Tobias-DG3YEV/RA-Sentinel/RASBB/Hardware/Rev.C/Design/Footprints/MMSZ5255BT1G.stp

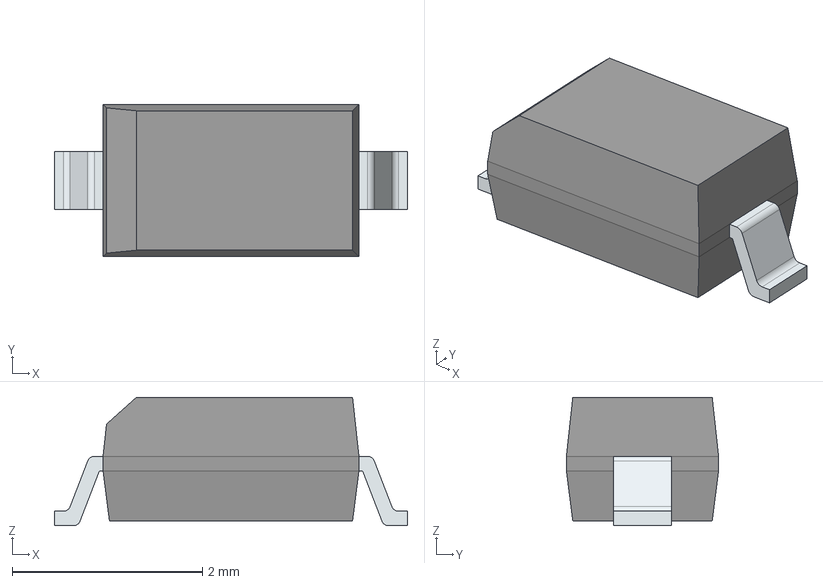
[picture p32: CAD file, 2026-08-13]
RASBB/Hardware/Rev.C/Design/Footprints/MMSZ5255BT1G.stp
3.71 x 1.60 x 1.35 mm
FilletPinL
FilletPinR
