Tobias-DG3YEV/RA-Sentinel/RASBB/Hardware/Rev.C/Design/Footprints/B340LB-13-F.stp

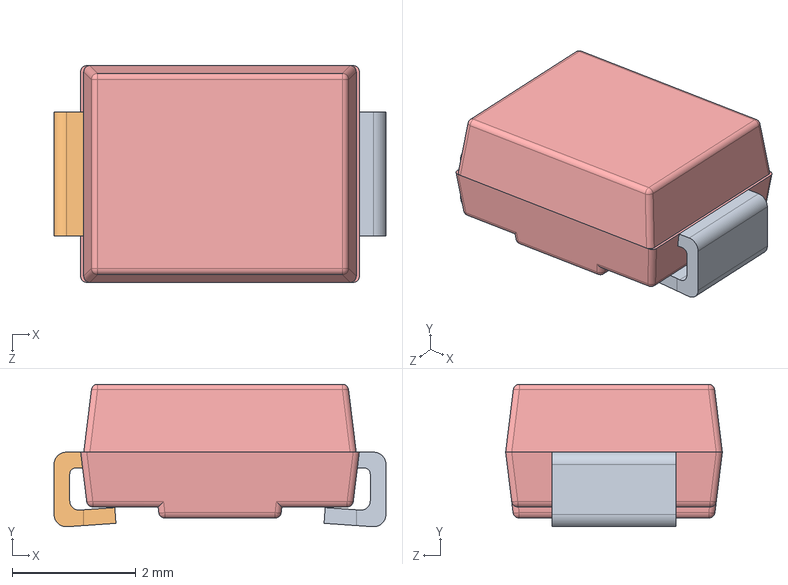
[picture p33: CAD file, 2026-08-13]
RASBB/Hardware/Rev.C/Design/Footprints/B340LB-13-F.stp
5.36 x 2.30 x 3.50 mm
LF 63010000599 RS2M
70mil 240 um RGPP
clip 63010000719 SQ0.45 H0.64 RS2M
SMB 16R compound RS2M
錨璃2^RS2M
