Tobias-DG3YEV/RA-Sentinel/RASBB/Hardware/Rev.C/Design/Footprints/VSSAF5L45HM3_A_H.stp

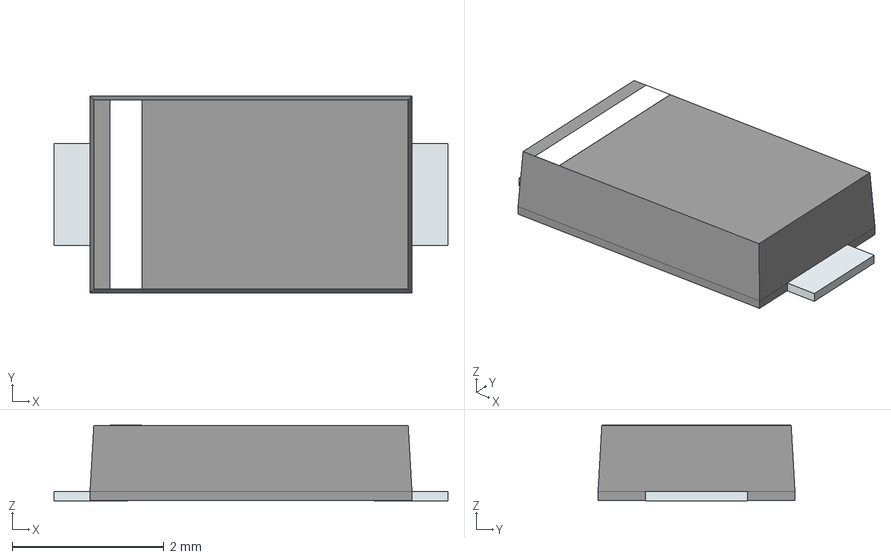
[picture p34: CAD file, 2026-08-13]
RASBB/Hardware/Rev.C/Design/Footprints/VSSAF5L45HM3_A_H.stp
5.20 x 2.60 x 1.00 mm
PinKIdent
PinK
PinA
