Tobias-DG3YEV/RA-Sentinel/RASBB/Hardware/Rev.C/Design/Footprints/BLM15BD601SH1D.stp

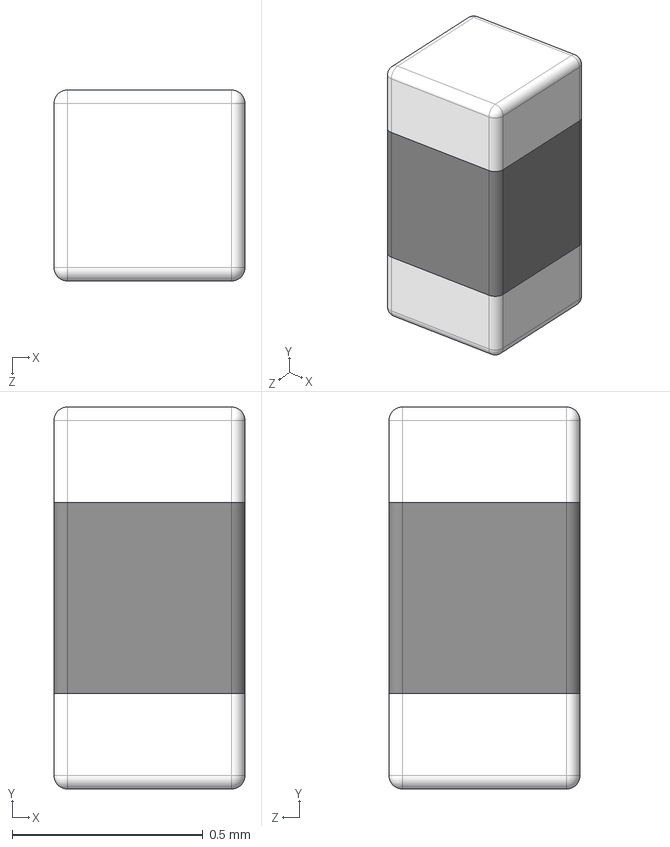
[picture p35: CAD file, 2026-08-13]
RASBB/Hardware/Rev.C/Design/Footprints/BLM15BD601SH1D.stp
0.5 x 1.00 x 0.5 mm
