Tobias-DG3YEV/RA-Sentinel/RASBB/Hardware/Rev.C/Design/Footprints/TS3A5018DBQR.stp

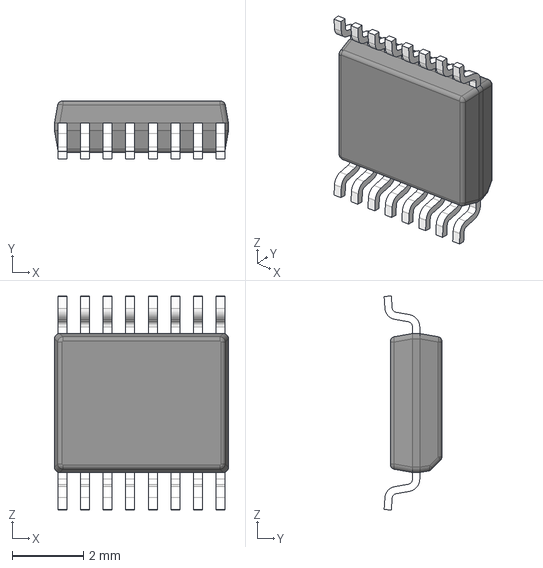
[picture p36: CAD file, 2026-08-13]
RASBB/Hardware/Rev.C/Design/Footprints/TS3A5018DBQR.stp
4.90 x 1.63 x 6.02 mm
BODY-SO
LEAD-DBQ0016B x 16
