Tobias-DG3YEV/RA-Sentinel/RASBB/Hardware/Rev.C/Design/Footprints/SDT5A60SA-13.stp

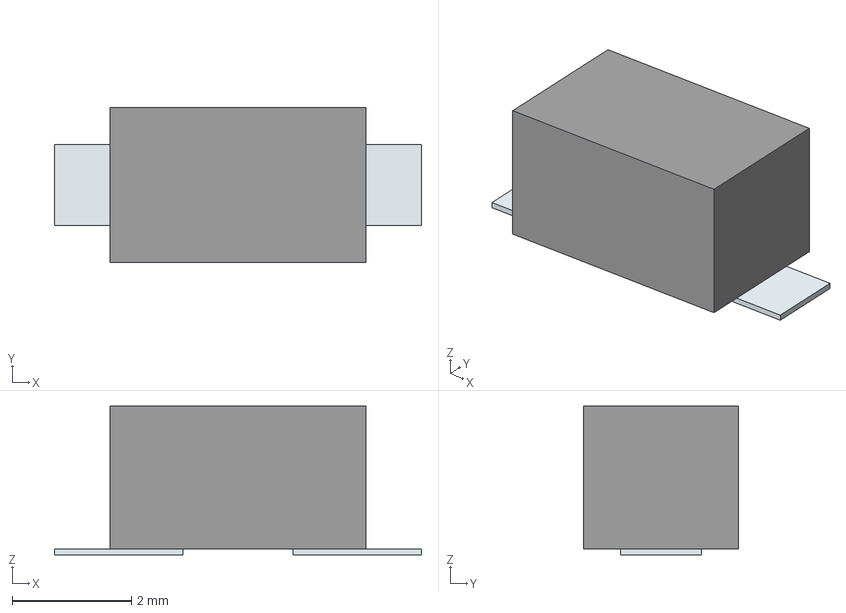
[picture p37: CAD file, 2026-08-13]
RASBB/Hardware/Rev.C/Design/Footprints/SDT5A60SA-13.stp
6.16 x 2.61 x 2.50 mm
Pins
