Tobias-DG3YEV/RA-Sentinel/RASBB/Hardware/Rev.C/Design/Footprints/SW_Wurth_WS-TASV_435451019820.step

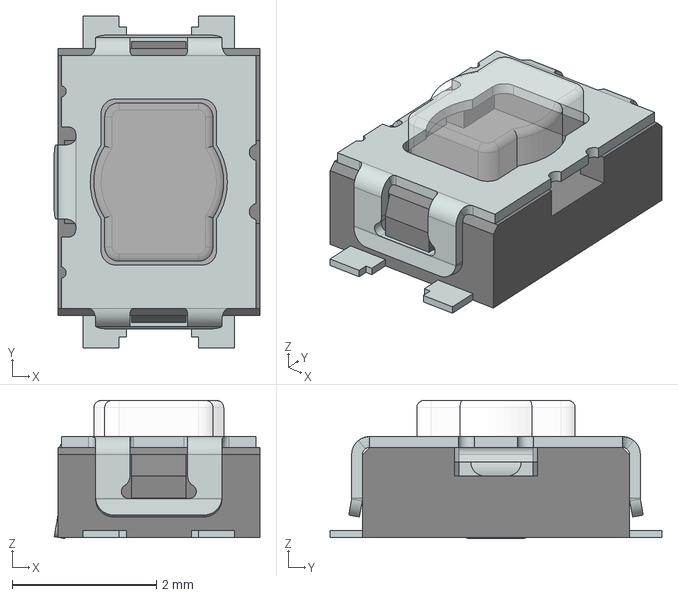
[picture p38: CAD file, 2026-08-13]
RASBB/Hardware/Rev.C/Design/Footprints/SW_Wurth_WS-TASV_435451019820.step
2.85 x 4.60 x 1.91 mm
