Tobias-DG3YEV/RA-Sentinel/RASBB/Hardware/Rev.C/Design/Footprints/XC7A100T-2CSG324I.stp

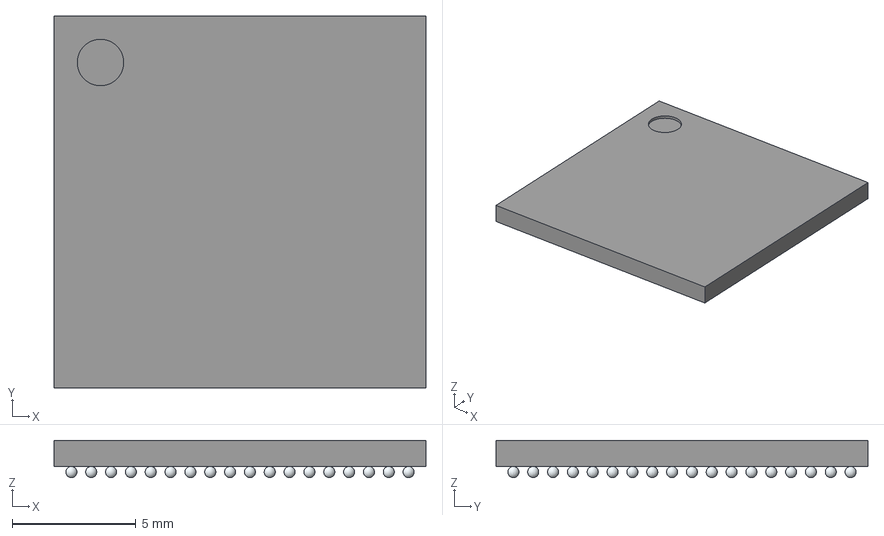
[picture p40: CAD file, 2026-08-13]
RASBB/Hardware/Rev.C/Design/Footprints/XC7A100T-2CSG324I.stp
15.0 x 15.0 x 1.50 mm
