Tobias-DG3YEV/RA-Sentinel/RASBB/Hardware/Rev.C/Design/Footprints/STP_MJ_HORIZONTAL_SHIELDED_W_LED _8P8C_TAB_UP_THR_615108137221R (rev1).stp

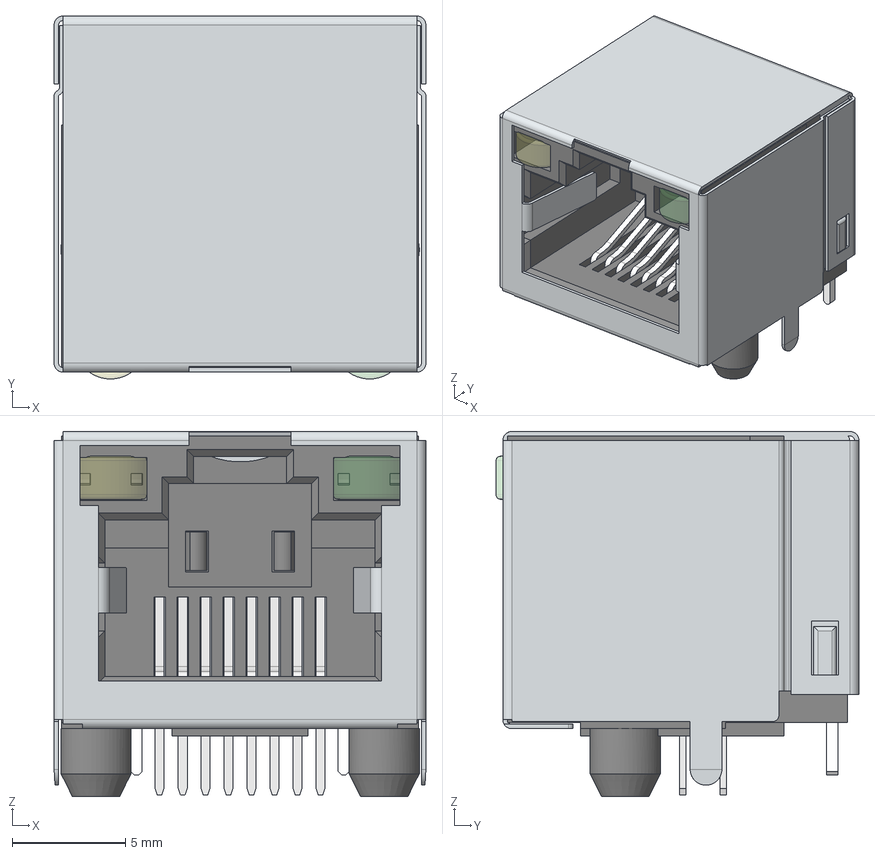
[picture p41: CAD file, 2026-08-13]
RASBB/Hardware/Rev.C/Design/Footprints/STP_MJ_HORIZONTAL_SHIELDED_W_LED _8P8C_TAB_UP_THR_615108137221R (rev1).stp
16.4 x 16.0 x 16.1 mm
615108137221R_Shielding
615108137221R_Housing
615108137221R_Pin Longue x 4
615108137221R_Pin Short x 4
615108137221R_Housing-2
615108137221R_Led Green
615108137221R_Led Yellow
