Tobias-DG3YEV/RA-Sentinel/RASBB/Software/RASBB_ECU/Core/Inc/lwipopts.h

/**
 * Copyright (C) 2017, STMicroelectronics, all right reserved.
 * Copyright (c) 2001-2004 Swedish Institute of Computer Science.
 * All rights reserved.
 *
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
 * This file is part of the lwIP TCP/IP stack.
 *
 * Author: Adam Dunkels <adam@sics.se>
 ******************************************************************************
 */

#ifndef __LWIPOPTS_H__
#define __LWIPOPTS_H__

/**
 * NO_SYS==1: Provides VERY minimal functionality. Otherwise,
 * use lwIP facilities.
 */
#define NO_SYS                  0

/*---------- Debug flags -----------*/
#define 	ETHARP_DEBUG    LWIP_DBG_OFF
#define 	UDP_DEBUG       LWIP_DBG_ON
#define PBUF_DEBUG        LWIP_DBG_OFF
#define MEM_STATS         1
#define   SO_REUSE        0

/* ---------- Memory options ---------- */
/* MEM_ALIGNMENT: should be set to the alignment of the CPU for which
   lwIP is compiled. 4 byte alignment -> define MEM_ALIGNMENT to 4, 2
   byte alignment -> define MEM_ALIGNMENT to 2. */
#define MEM_ALIGNMENT           4

/* MEM_SIZE: the size of the heap memory. If the application will send
a lot of data that needs to be copied, this should be set high. */
#define MEM_SIZE                (24*1024)

/* Relocate the LwIP RAM heap pointer */
#define LWIP_RAM_HEAP_POINTER    (0x30004000)

/* MEMP_NUM_TCP_PCB: the number of simulatenously active TCP
   connections. */
#define MEMP_NUM_TCP_PCB        20

#define MEMP_NUM_NETCONN		8

/* MEMP_NUM_TCP_SEG: the number of simultaneously queued TCP
   segments. */
#define MEMP_NUM_TCP_SEG        TCP_SND_QUEUELEN

/* ---------- Pbuf options ---------- */
/* PBUF_POOL_SIZE: the number of buffers in the pbuf pool.
   @ note: used to allocate Tx pbufs only */

/* PBUF_POOL_BUFSIZE: the size of each pbuf in the pbuf pool. */
#define PBUF_POOL_BUFSIZE       1536

/* LWIP_SUPPORT_CUSTOM_PBUF == 1: to pass directly MAC Rx buffers to the stack
   no copy is needed */
#define LWIP_SUPPORT_CUSTOM_PBUF      1

/* ---------- IPv4 options ---------- */
#define LWIP_IPV4                1

/* ---------- TCP options ---------- */
#define LWIP_TCP                1
#define TCP_TTL                 255

/* Controls if TCP should queue segments that arrive out of
   order. Define to 0 if your device is low on memory. */

/* TCP Maximum segment size. */
#define TCP_MSS                 (1500 - 40)	  /* TCP_MSS = (Ethernet MTU - IP header size - TCP header size) */

/* TCP sender buffer space (bytes). */
#define TCP_SND_BUF             (4*TCP_MSS)


/* TCP receive window. */
#define TCP_WND                 (4*TCP_MSS)


/* ---------- ICMP options ---------- */
#define LWIP_ICMP                       1


/* ---------- DHCP options ---------- */
#define LWIP_DHCP               0


/* ---------- UDP options ---------- */
#define LWIP_UDP                1
#define UDP_TTL                 255

#define LWIP_IGMP                       1

/* ---------- Statistics options ---------- */
#define LWIP_STATS 				1

/* ---------- link callback options ---------- */
/* LWIP_NETIF_LINK_CALLBACK==1: Support a callback function from an interface
 * whenever the link changes (i.e., link down)
 */
#define LWIP_NETIF_LINK_CALLBACK        0

/*
   --------------------------------------
   ---------- Checksum options ----------
   --------------------------------------
*/

/*
The STM32H7xx allows computing and verifying the IP, UDP, TCP and ICMP checksums by hardware:
 - To use this feature let the following define uncommented.
 - To disable it and process by CPU comment the  the checksum.
*/
#define CHECKSUM_BY_HARDWARE


#ifdef CHECKSUM_BY_HARDWARE
  /* CHECKSUM_GEN_IP==0: Generate checksums by hardware for outgoing IP packets.*/
  #define CHECKSUM_GEN_IP                 0
  /* CHECKSUM_GEN_UDP==0: Generate checksums by hardware for outgoing UDP packets.*/
  #define CHECKSUM_GEN_UDP                0
  /* CHECKSUM_GEN_TCP==0: Generate checksums by hardware for outgoing TCP packets.*/
  #define CHECKSUM_GEN_TCP                0
  /* CHECKSUM_CHECK_IP==0: Check checksums by hardware for incoming IP packets.*/
  #define CHECKSUM_CHECK_IP               0
  /* CHECKSUM_CHECK_UDP==0: Check checksums by hardware for incoming UDP packets.*/
  #define CHECKSUM_CHECK_UDP              0
  /* CHECKSUM_CHECK_TCP==0: Check checksums by hardware for incoming TCP packets.*/
  #define CHECKSUM_CHECK_TCP              0
  /* CHECKSUM_GEN_ICMP==1: Check checksums by hardware for outgoing ICMP packets.*/
  /* Hardware TCP/UDP checksum insertion not supported when packet is an IPv4 fragment */
  #define CHECKSUM_GEN_ICMP               1
  /* CHECKSUM_CHECK_ICMP==0: Check checksums by hardware for incoming ICMP packets.*/
  #define CHECKSUM_CHECK_ICMP             0

#else
  /* CHECKSUM_GEN_IP==1: Generate checksums in software for outgoing IP packets.*/
  #define CHECKSUM_GEN_IP                 1
  /* CHECKSUM_GEN_UDP==1: Generate checksums in software for outgoing UDP packets.*/
  #define CHECKSUM_GEN_UDP                1
  /* CHECKSUM_GEN_TCP==1: Generate checksums in software for outgoing TCP packets.*/
  #define CHECKSUM_GEN_TCP                1
  /* CHECKSUM_CHECK_IP==1: Check checksums in software for incoming IP packets.*/
  #define CHECKSUM_CHECK_IP               1
  /* CHECKSUM_CHECK_UDP==1: Check checksums in software for incoming UDP packets.*/
  #define CHECKSUM_CHECK_UDP              1
  /* CHECKSUM_CHECK_TCP==1: Check checksums in software for incoming TCP packets.*/
  #define CHECKSUM_CHECK_TCP              1
  /* CHECKSUM_GEN_ICMP==1: Check checksums by hardware for outgoing ICMP packets.*/
  #define CHECKSUM_GEN_ICMP               1
  /* CHECKSUM_CHECK_ICMP==1: Check checksums by hardware for incoming ICMP packets.*/
  #define CHECKSUM_CHECK_ICMP             1
#endif


/*
   ----------------------------------------------
   ---------- Sequential layer options ----------
   ----------------------------------------------
*/
/**
 * LWIP_NETCONN==1: Enable Netconn API (require to use api_lib.c)
 */
#define LWIP_NETCONN                    1

/*
   ------------------------------------
   ---------- Socket options ----------
   ------------------------------------
*/
/**
 * LWIP_SOCKET==1: Enable Socket API (require to use sockets.c)
 */
#define LWIP_SOCKET                     0

/*
   ------------------------------------
   ---------- httpd options ----------
   ------------------------------------
*/
/** Set this to 1 to include "fsdata_custom.c" instead of "fsdata.c" for the
 * file system (to prevent changing the file included in CVS) */
#define HTTPD_USE_CUSTOM_FSDATA   1
#define MEMP_DEBUG LWIP_DBG_ON
#define MEM_DEBUG LWIP_DBG_ON

/*
   ---------------------------------
   ---------- OS options ----------
   ---------------------------------
*/

#define TCPIP_THREAD_NAME              "TCP/IP"
#define TCPIP_THREAD_STACKSIZE          2048
#define TCPIP_MBOX_SIZE                 6
#define DEFAULT_UDP_RECVMBOX_SIZE       6
#define DEFAULT_TCP_RECVMBOX_SIZE       6
#define DEFAULT_ACCEPTMBOX_SIZE         6
#define DEFAULT_THREAD_STACKSIZE        1024
#define TCPIP_THREAD_PRIO               osPriorityHigh

#endif /* __LWIPOPTS_H__ */
