Tobias-DG3YEV/RA-Sentinel/RASBB/Software/RASBB_ECU/Core/Inc/main.h

#define IP_ADDR0   ((uint8_t)10U)
#define IP_ADDR1   ((uint8_t)0U)
#define IP_ADDR2   ((uint8_t)10U)
#define IP_ADDR3   ((uint8_t)77U)
#define NETMASK_ADDR0   ((uint8_t)255U)
#define NETMASK_ADDR1   ((uint8_t)255U)
#define NETMASK_ADDR2   ((uint8_t)0U)
#define NETMASK_ADDR3   ((uint8_t)0U)
#define GW_ADDR0   ((uint8_t)10U)
#define GW_ADDR1   ((uint8_t)0U)
#define GW_ADDR2   ((uint8_t)13U)
#define GW_ADDR3   ((uint8_t)1U)
#define UPNP_PORT	4842
#define ETH_RESET_Pin GPIO_PIN_0
#define ETH_RESET_GPIO_Port GPIOB
#define SPI3_NCS_Pin GPIO_PIN_2
#define SPI3_NCS_GPIO_Port GPIOD
