Tobias-DG3YEV/RA-Sentinel/OWIFI_RX/owifi.srcs/sources_1/link_supervisor.v

////////////////////////////////////////////////////////////////////////////////
// Design Name: OWIFI_RX
// Module Name: link_supervisor.v
// Project Name: Radio Access Sentinel
// Engineer: Tobias Weber
// Target Devices: Artix-7 XC7A100T (RASBB U10)
// Tool Versions: Vivado 2025.2
// Description:  RA-Sentinel is a WiFi activity and threat detection platform
//
// Additional Comments: https://github.com/Tobias-DG3YEV/RA-Sentinel
//
// This project was funded through the NGI0 Entrust Fund, a fund established
// by NLnet with financial support from the European Commission's
// Next Generation Internet programme, under the aegis of DG Communications
// Networks, Content and Technology under grant agreement No 101069594.
// https://nlnet.nl/project/RA-Sentinel/
//
// SPDX-FileCopyrightText: 2026 Tobias Weber
// SPDX-License-Identifier: GPL-3.0-only
//
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
// Per-ADC LVDS link supervisor: owns the data-path IDELAY tap and keeps the
// link locked ACROSS MASTER-CLOCK CHANGES, using the continuously available
// FCLK-word decode as the health metric (i_hit: "the deserialized FCLK word
// matched the frame pattern at some window base this word" - see top.v).
// No ADC test pattern involved, so this works during normal operation.
//
// Why retraining is needed at all: the ADC bit clock reaches the ISERDES
// through general fabric routing whose insertion delay is constant in ns,
// while the serial UI scales with the front-end's master clock. Tuning the
// TCXO/external reference from 40MHz towards 38 or 42MHz therefore slides
// the ODD-path sampling point across (and eventually past) the data eye -
// the link then "loses bit lock" and the panes fill with full-scale noise.
// The IDELAY tap can pull the sampling point back; this FSM notices the
// degradation (FCLK decode misses) and re-sweeps automatically.
//
//   SWEEP  try all 32 taps; per tap, count decode misses over WIN_CE words
//          after SETTLE_CE settle. A tap is "good" if misses <= GOOD_MAX.
//          Commit the CENTER of the longest run of good taps (max margin
//          both directions -> max tolerated frequency excursion before the
//          next retrain). No good tap at all -> commit the minimum-miss tap
//          and retry after the long FAIL_HOLD_CE backoff.
//   MON    count misses per WIN_CE window. BAD_WINS consecutive windows
//          above MISS_MAX -> back to SWEEP. A GRACE_WINS grace period after
//          each sweep lets the rotation decode re-lock and the counters
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
